kurtjd/CHIPnGo/images/current_status_4.jpg

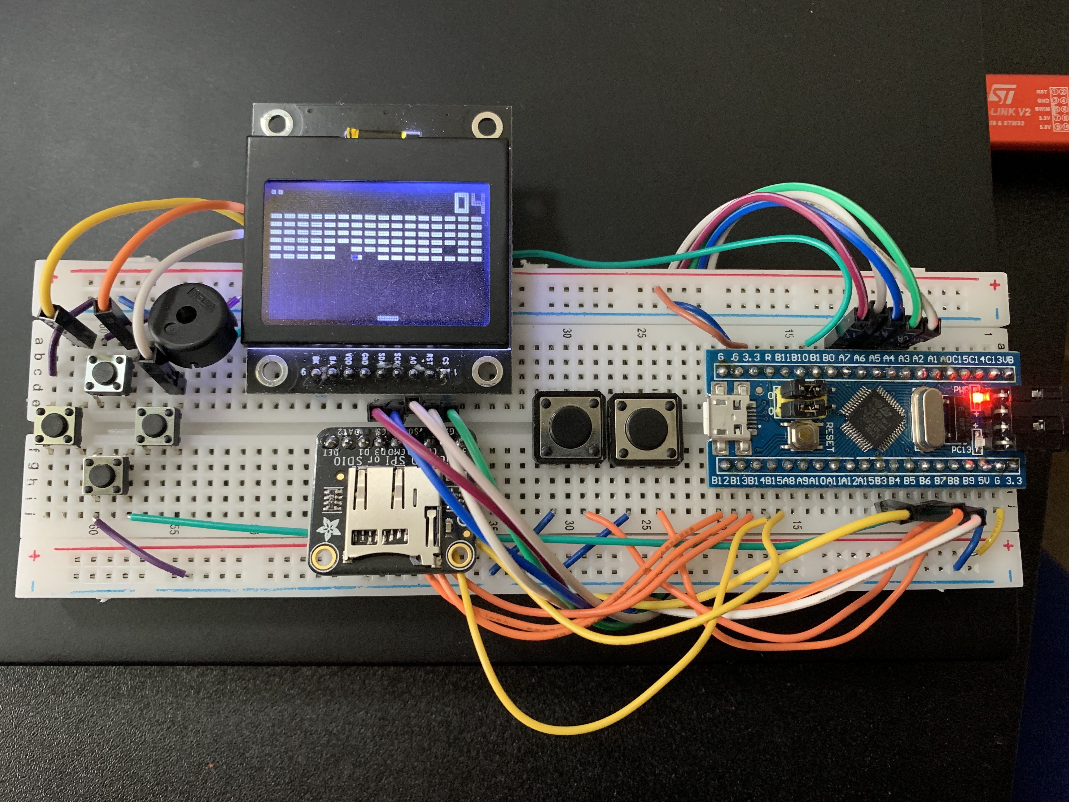
images/current_status_4.jpg
