kurtjd/CHIPnGo/src/display.c

#include "display.h"

#include <ctype.h>

#include "delay.h"
#include "gpio.h"

// CS: B12
// SCK: B13
// A0: A8
// SDA: B15
// RST: B14

#define SPI_CLK (1 << 14)
#define SPI2_START 0x40003800
#define SPI2_CR1 (*((volatile uint32_t *)(SPI2_START + 0x00)))
#define SPI2_CR2 (*((volatile uint32_t *)(SPI2_START + 0x04)))
#define SPI2_SR (*((volatile uint32_t *)(SPI2_START + 0x08)))
#define SPI2_DR (*((volatile uint32_t *)(SPI2_START + 0x0C)))

#define A0 (1 << 8)
#define RST (1 << 14)

#define SET_PAGE_ADDR 0xB0
#define SET_COL_ADDR_MSB 0x10
#define SET_COL_ADDR_LSB 0x0
#define DISPLAY_ON 0xAF
#define DISPLAY_OFF 0xAE

#define NUM_COLS 128
#define NUM_PAGES 8

#define CHAR_WIDTH 5
#define CHAR_HEIGHT 5

static const uint8_t NUM_FONT[][CHAR_WIDTH] = {
    {0x0E, 0x11, 0x11, 0x11, 0x0E},  // 0
    {0x00, 0x01, 0x1F, 0x00, 0x00},  // 1
    {0x12, 0x19, 0x15, 0x12, 0x00},  // 2
    {0x11, 0x15, 0x15, 0x15, 0x1F},  // 3
    {0x07, 0x04, 0x04, 0x04, 0x1F},  // 4
    {0x16, 0x15, 0x15, 0x15, 0x1D},  // 5
    {0x1F, 0x15, 0x15, 0x15, 0x1D},  // 6
    {0x11, 0x09, 0x05, 0x03, 0x00},  // 7
    {0x1B, 0x15, 0x15, 0x1B, 0x00},  // 8
    {0x17, 0x15, 0x15, 0x1F, 0x00}   // 9
};

static const uint8_t ALPHA_FONT[][CHAR_WIDTH] = {
    {0x1F, 0x05, 0x05, 0x05, 0x1F},  // A
    {0x1F, 0x15, 0x15, 0x15, 0x0E},  // B
    {0x1F, 0x11, 0x11, 0x11, 0x11},  // C
    {0x1F, 0x11, 0x11, 0x11, 0x0E},  // D
    {0x1F, 0x15, 0x15, 0x15, 0x11},  // E
    {0x1F, 0x05, 0x05, 0x05, 0x01},  // F
    {0x1F, 0x11, 0x15, 0x15, 0x1D},  // G
    {0x1F, 0x04, 0x04, 0x04, 0x1F},  // H
    {0x11, 0x11, 0x1F, 0x11, 0x11},  // I
    {0x19, 0x11, 0x1F, 0x01, 0x00},  // J
    {0x1F, 0x04, 0x0A, 0x11, 0x00},  // K
    {0x1F, 0x10, 0x10, 0x10, 0x00},  // L
    {0x1F, 0x02, 0x04, 0x02, 0x1F},  // M
    {0x1F, 0x02, 0x04, 0x08, 0x1F},  // N
    {0x1F, 0x11, 0x11, 0x11, 0x1F},  // O
    {0x1F, 0x05, 0x05, 0x05, 0x07},  // P
    {0x1F, 0x11, 0x11, 0x19, 0x1F},  // Q
    {0x1F, 0x05, 0x05, 0x0D, 0x17},  // R
    {0x17, 0x15, 0x15, 0x15, 0x1D},  // S
    {0x01, 0x01, 0x1F, 0x01, 0x01},  // T
    {0x1F, 0x10, 0x10, 0x10, 0x1F},  // U
    {0x03, 0x0C, 0x10, 0x0C, 0x03},  // V
    {0x1F, 0x10, 0x08, 0x10, 0x1F},  // W
    {0x11, 0x0A, 0x04, 0x0A, 0x11},  // X
    {0x01, 0x02, 0x1C, 0x02, 0x01},  // Y
    {0x11, 0x19, 0x15, 0x13, 0x11}   // Z
};

static const uint8_t NO_CHAR[][CHAR_WIDTH] = {{0}};

static const uint8_t LEFT_ARROW[] = {0x00, 0x00, 0x04, 0x0E, 0x1F};
static const uint8_t RIGHT_ARROW[] = {0x1F, 0x0E, 0x04, 0x00, 0x00};

static const uint8_t *_char_to_bits(char c) {
    switch (c) {
        case '<':
            return LEFT_ARROW;
        case '>':
            return RIGHT_ARROW;
    }

    c = toupper(c);
    if (c >= '0' && c <= '9') {
        return NUM_FONT[c - '0'];
    } else if (c >= 'A' && c <= 'Z') {
        return ALPHA_FONT[c - 'A'];
    } else {
        return NO_CHAR[0];
    }
}

static void _gpio_init(void) {
    // Disable reset state
    GPIOA_CRH &= ~(1 << 2);
    GPIOB_CRH &= ~((1 << 18) | (1 << 22) | (1 << 26) | (1 << 30));

    // MODEy (A8, B12, B13, B14, B15 2MHz out)
    GPIOA_CRH |= (1 << 1);
    GPIOB_CRH |= ((1 << 17) | (1 << 21) | (1 << 25) | (1 << 29));

    // CNFy (B12, B13, B15 alt out, A8, B14 gpo)
    GPIOB_CRH |= ((1 << 19) | (1 << 23) | (1 << 31));
}

static void _spi_init(void) {
    RCC_APB1ENR |= SPI_CLK;
    for (volatile int i = 0; i < 10; i++)
        ;

    SPI2_CR1 |= (3 << 3);   // CLK / 16 (fastest speed that works)
    SPI2_CR2 |= (1 << 2);   // Enable SS output
    SPI2_CR1 |= (1 << 15);  // 1 line mode
    SPI2_CR1 |= (1 << 14);  // Transmit-only
    SPI2_CR1 |= (1 << 2);   // Set as master
    SPI2_CR1 |= (1 << 6);   // Enable
}

static void _display_write(uint8_t data) {
    SPI2_DR = data;
    while (!(SPI2_SR & 0x02))
        ;
    for (volatile int i = 0; i < 10; i++)
        ;  // Need a very brief delay
}

static void _display_putc(uint8_t x, uint8_t y, char c) {
    display_send_cmd(SET_COL_ADDR_MSB | (x >> 4));
    display_send_cmd(SET_COL_ADDR_LSB | (x & 0x0F));

    for (int i = 0; i < CHAR_WIDTH; i++) {
        display_send_data(_char_to_bits(c)[i]);
    }
}

void display_init(void) {
    _gpio_init();

    // Perform hardware reset of display
    GPIOB_ODR &= ~RST;
    delay(5);
    GPIOB_ODR |= RST;
    delay(1);

    _spi_init();

    // Voltage stuff
    // Not entirely sure why this is needed
    // Couldn't find much explanation in datasheet
    display_send_cmd(0x28 | 0x7);

    // Zero out display RAM and turn on
    display_clear();
    display_send_cmd(DISPLAY_ON);
}

void display_send_data(uint8_t data) {
    GPIOA_ODR |= A0;
    _display_write(data);
}

void display_send_cmd(uint8_t cmd) {
    GPIOA_ODR &= ~A0;
    _display_write(cmd);
}

void display_clear(void) {
    for (int y = 0; y < NUM_PAGES; y++) {
        display_send_cmd(SET_PAGE_ADDR | y);
        display_send_cmd(SET_COL_ADDR_MSB);
        display_send_cmd(SET_COL_ADDR_LSB);

        for (int x = 0; x < NUM_COLS; x++) {
            display_send_data(0x00);
        }
    }
}

void display_draw(uint8_t buf[64][16]) {
    for (int y = 0; y < NUM_PAGES; y++) {
        display_send_cmd(SET_PAGE_ADDR | y);
        display_send_cmd(SET_COL_ADDR_MSB);
        display_send_cmd(SET_COL_ADDR_LSB);

        for (int x = 0; x < NUM_COLS; x++) {
            int row = NUM_PAGES * y;
            uint8_t data = 0;

            for (int i = 0; i < 8; i++) {
                uint8_t bit = (buf[row + i][x / 8]) & (1 << (7 - (x % 8)));

                if (bit) {
                    data |= (1 << i);
                }
            }

            display_send_data(data);
        }
    }
}

void display_print(uint8_t x, uint8_t y, const char *str) {
    display_send_cmd(SET_PAGE_ADDR | y);

    for (int i = 0; str[i] != 0; i++) {
        _display_putc(x + (i * (CHAR_WIDTH + 1)), y, str[i]);
    }
}

void display_test(void) {
    for (int y = 0; y < NUM_PAGES; y++) {
        display_send_cmd(SET_PAGE_ADDR | y);
        display_send_cmd(SET_COL_ADDR_MSB);
        display_send_cmd(SET_COL_ADDR_LSB);

        for (int x = 0; x < NUM_COLS; x++) {
            display_send_data(0xFF);
            delay(50);
        }
    }
}

void display_font_test(void) {
    display_print(35, 3, "0123456789");
    display_print(25, 4, "ABCDEFGHIJKLM");
    display_print(25, 5, "NOPQRSTUVWXYZ");
    delay(5000);
}
